TheProfessionnal/InfoClock/InfoClock-master/src/DisplayTask.cpp

/*
 * DisplayTask.cpp
 *
 *  Created on: 15.02.2017
 *      Author: Bartosz Bielawski
 */


#include "DisplayTask.hpp"

#include "pyfont.h"
#include "myTestFont8.h"

#include "utils.h"
#include "tasks_utils.h"
#include "DataStore.h"

#include "config.h"


DisplayTask::DisplayTask():
		TaskCRTP(&DisplayTask::nextMessage),
		ledMatrixDriver(
				readConfigWithDefault(F("segments"), "8").toInt(), LED_CS,
				readConfigWithDefault(F("rotation"), "0").toInt()),
				scroll(ledMatrixDriver),
		regularMessages({
			{this, getDate, 2_s,	1,	false},
			})
{
	init();
	ledMatrixDriver.setIntensity(readConfig(F("brightness")).toInt());
}


void DisplayTask::addClock()
{
	DisplayState ds = {this, getTime, 1_s, 5,	false};
	regularMessages.push_back(ds);
}


void DisplayTask::addRegularMessage(const DisplayState& ds)
{
	regularMessages.push_back(ds);
	addClock();
}

void DisplayTask::removeRegularMessages(void* owner)
{
	regularMessages.erase(
			std::remove_if(
					regularMessages.begin(),
					regularMessages.end(),
					[owner] (const DisplayState& ds) {return ds.owner == owner;}));
}

void DisplayTask::init()
{
	index = regularMessages.size()-1;
}

void DisplayTask::reset()
{
	init();
}


void DisplayTask::pushMessage(const String& m, uint16_t sleep, bool scrolling)
{
	priorityMessages.push_back(DisplayState{this, [m](){return m;}, sleep, 1, scrolling});

	//wake up thread and interrupt the other display
	//only if it's not a priority message
	if (!priorityMessagePlayed)
	{
		nextState = &DisplayTask::nextMessage;
		resume();
	}
}

void DisplayTask::scrollMessage()
{
	bool done = scroll.tick();
	sleep(ds.period);

	if (done)
	{
		logPrintfX(F("DT"), F("Scrolling done..."));
		nextState = &DisplayTask::nextMessage;
	}
}

void DisplayTask::nextMessage()
{
	//load the next display
	nextDisplay();

	if (ds.scrolling)
	{		
		scroll.renderString(currentMessage, myTestFont::font);
		nextState = &DisplayTask::scrollMessage;
		return;
	}

	nextState = &DisplayTask::refreshMessage;
}


void DisplayTask::refreshMessage()
{
	//this code here calls the function again and again because the message may be different every time
	//for example the time or date

	scroll.renderString(ds.fun(), myTestFont::font);

	if (--ds.cycles == 0)
		nextState = &DisplayTask::nextMessage;

	sleep(ds.period);
	//this flag will allow slow tasks to execute only if there is a two second sleep ahead
	slowTaskCanExecute = ds.period >= 1_s;
}


void DisplayTask::nextDisplay()
{
	//special case for priority messages
	if (priorityMessages.size())
	{
		ds = priorityMessages.front();
		priorityMessages.erase(priorityMessages.begin());
		currentMessage = ds.fun();
		
		logPrintfX(F("DT"), F("New message from PQ = %s"), currentMessage.c_str());
		priorityMessagePlayed = true;
		return;
	}

	priorityMessagePlayed = false;
	//otherwise get back to the regular display
		
	if (regularMessages.size() == 0)		
		return;
		
	do
	{
		index++;
		index %= regularMessages.size();
		ds = regularMessages[index];

		// save the current message for future use
		currentMessage = ds.fun();
	}
	while (currentMessage.length() == 0);	

	logPrintfX(F("DT"), F("New message from RQ = %s"), currentMessage.c_str());
	ledMatrixDriver.setIntensity(readConfig(F("brightness")).toInt());
}

DisplayTask& DisplayTask::getInstance()
{
	static DisplayTask displayTask;
	return displayTask;
}
