TheProfessionnal/InfoClock/InfoClock-master/src/WebServerTask.cpp

/*
 * WebServerTask.cpp
 *
 *  Created on: 10.01.2017
 *      Author: Bartosz Bielawski
 */

#include "Arduino.h"
#include "time.h"
#include "LittleFS.h"


#include "WebServerTask.h"
#include "ESP8266WebServer.h"
#include "ESP8266HTTPUpdateServer.h"
#include "ArduinoOTA.h"

#include "MacroStringReplace.h"
#include "config.h"
#include "DataStore.h"

#include "html/webpage.h"

#include "utils.h"
#include "tasks_utils.h"
#include "web_utils.h"
#include "LambdaTask.hpp"



WebServerTask::WebServerTask():
		webServer(80)
{
	reset();
	DisplayState ds{this, [this]() {return webmessage;}, 0.05_s, 1, true};
	addRegularMessage(ds);
}

void WebServerTask::registerPage(const String& url, const String& label,
		std::function<void(ESP8266WebServer& ws)> ph)
{
	registeredPages.emplace_back(url, label);
	String newUrl("/");
	newUrl += url;
	std::function<void(void)> f = [this, ph] () {ph(webServer);};
	webServer.on(newUrl.c_str(), f);
}

void WebServerTask::reset()
{
	webServer.stop();
	sleep(5_s);
	started = false;

	webmessage = "";
	webmessageIP = "";
}


void WebServerTask::run()
{
	if (!started)
	{
		started = true;
		logPrintfX(F("WST"), F("Configuring server"));

		webServer.onNotFound([this](){
			webServer.send(404, "text/plain", "Not found... :/");
		});

		webServer.on("/", [this](){
			handleMainPage();
		});

		webServer.on("/webmessage", [this](){handleWebMessage();});
		webServer.on("/status", 	[this](){handleStatus();});
		webServer.on("/reset", [this]{handleReset();});
		webServer.on("/config", [this]{handleConfig();});
		webServer.on("/log", [this](){handleLogs();});

		webServer.begin();

		logPrintfX(F("WST"), F("Ready!"));
		return;
	}

	webServer.handleClient();
	delay(0);
}

String WebServerTask::generateLinks()
{
	String results;

	for (auto& p: registeredPages)
	{
		results += "<a href=\"";
		results += p.first;
		results += "\">";
		results += p.second;
		results += "</a>\n";
	}

	return results;
}

FlashStream mainPageFS(mainPage);

void WebServerTask::handleMainPage()
{
	StringStream ss(2048);
	macroStringReplace(mainPageFS, [this] (const char*) {return generateLinks();}, ss);
	webServer.send(200, textHtml, ss.buffer);
}

FlashStream statusFS(statusPage);

void WebServerTask::handleStatus()
{
	StringStream ss(2048);
	macroStringReplace(pageHeaderFS, constString("Status"), ss);
	macroStringReplace(statusFS, dataSource, ss);
	webServer.send(200, textHtml, ss.buffer);
}


void WebServerTask::handleReset()
{
	if (!handleAuth(webServer)) return;

	rebootClock();

	webServer.sendHeader("Location", String("/"), true);
	webServer.send(302, textPlain, "");
}

void WebServerTask::handleLogs()
{
	if (!handleAuth(webServer)) return;

	StringStream ss(2048);
	webServer.chunkedResponseModeStart(200, "text/html");
	macroStringReplace(pageHeaderFS, constString("Logs"), ss);
	webServer.sendContent(ss.buffer);
	
	webServer.sendContent(F("<table>"));
	for (const auto& s: getLogHistory())
	{
		webServer.sendContent(F("<tr><td>"));
		webServer.sendContent(s);
		webServer.sendContent(F("</td></tr>\n\r"));
		
	}
	webServer.sendContent(F("</table><script>setTimeout(function(){window.location.reload(1);}, 5000);</script></body></html>"));
	webServer.chunkedResponseFinalize();
}

FlashStream webmessageFS(webmessagePage);

void WebServerTask::handleWebMessage()
{
	if (!handleAuth(webServer))
		return;

	if (webServer.method() == HTTP_POST)
	{
		auto wm = webServer.arg(F("webmessage"));
		
		webmessage = wm;
		webmessageIP = webServer.client().remoteIP().toString();
		logPrintfX(F("WST"),
				   F("New webmessage %s from %s"),
				   wm.c_str(),
				   webmessageIP.c_str());
	}

	StringStream ss(2048);

	macroStringReplace(pageHeaderFS, constString(F("Webmessage")), ss);
	macroStringReplace(webmessageFS, constString(webmessage), ss);

	webServer.send(200, textHtml, ss.buffer);
}

FlashStream configPageFS(configPage);

void WebServerTask::handleConfig()
{
	if (!handleAuth(webServer))
		return;

	String content;

	if (webServer.method() == HTTP_GET)
	{
		//read config from the file
		LittleFS.begin();
		auto file = LittleFS.open("/config.txt", "r");
		if (!file)
			content = F("# The file is empty, please create a new one!");
		else
		{
			content = file.readString();
			file.close();
		}
	
		LittleFS.end();
	}
	else
	{
		//POST
		//load content from variable
		content = webServer.arg(F("content"));
		LittleFS.begin();
		auto file = LittleFS.open("/config.txt", "w+");
		file.print(content);
		file.close();
		LittleFS.end();
		readConfigFromFS();
	}
	
	StringStream ss(2048);
	macroStringReplace(pageHeaderFS, constString(F("Config")), ss);
	macroStringReplace(configPageFS, constString(content), ss);
	webServer.send(200, textHtml, ss.buffer);
}

WebServerTask& WebServerTask::getInstance()
{
	static WebServerTask webServer;
	return webServer;
}
