TheProfessionnal/InfoClock/InfoClock-master/src/OTA.cpp

/*
 * OTA.cpp

 *
 *  Created on: 17.04.2017
 *      Author: caladan
 */

#include "Arduino.h"
#include "ArduinoOTA.h"
#include "pgmspace.h"
#include "OTA.hpp"
#include "utils.h"
#include "ESP8266mDNS.h"

void configureOTA()
{
	ArduinoOTA.onStart([]() {
		logPrintfX(F("OTA"), F("Starting..."));
	});

	ArduinoOTA.onEnd([]() {
		logPrintfX(F("OTA"), F("Done..."));
	});

	ArduinoOTA.onProgress([](unsigned int progress, unsigned int total) {
		logPrintfX(F("OTA"), F("Progress: %u%%"), (progress / (total / 100)));
	});
	ArduinoOTA.onError([](ota_error_t error) {
		logPrintfX(F("OTA"), F("Error[%u]"), error);
	});

	ArduinoOTA.setPassword(readConfig(F("configPassword")).c_str());

	ArduinoOTA.begin();
}
