TheProfessionnal/InfoClock/InfoClock-master/src/WeatherGetter.h

/*
 * WeatherGetter.h
 *
 *  Created on: 04.01.2017
 *      Author: Bartosz Bielawski
 */

#ifndef WEATHERGETTER_H_
#define WEATHERGETTER_H_

#include <tasks.hpp>
#include "ESP8266HTTPClient.h"
#include <vector>

#include <ESP8266WebServer.h>
class WeatherGetter: public Tasks::Task
{
	public:
		WeatherGetter();
		virtual ~WeatherGetter() {}
		virtual void reset();
		virtual void run();
	private:
		struct Weather
		{
			Weather(uint32_t locationId):
				locationId(locationId),
				temperature(0),
				temperatureForecast(0) {}

			uint32_t locationId;
			float  temperature;
			float  temperatureForecast;
			String description;
			String location;

		};

		std::vector<Weather> weathers;

		uint32_t currentWeatherIndex;

		String apiKey;

		//page handling
		void handleConfig(ESP8266WebServer& ws);
		void handleStatus(ESP8266WebServer& ws);

		//display function
		String getWeatherDescription();
};

#endif /* WEATHERGETTER_H_ */
