TheProfessionnal/InfoClock/InfoClock-master/src/myTestFont8.h

#ifndef myTestFont8_H
#define myTestFont8_H

#include "pyfont.h"

namespace myTestFont
{
    const uint8_t data[] =
    {
			0x00, 0x00, 0xBF, 0x03, 0x01, 0x03, 0x14, 0x3E, 0x14, 0x3E, 0x14, 0x2C, 0x7E, 0x34, 0x24, 0x10,
			0x08, 0x24, 0x60, 0x90, 0x90, 0x60, 0xF0, 0x10, 0x10, 0xE0, 0x90, 0x90, 0xFC, 0x03, 0x7E, 0x81,
			0x81, 0x7E, 0x14, 0x08, 0x14, 0x08, 0x08, 0x3E, 0x08, 0x08, 0xC0, 0x08, 0x08, 0x08, 0x80, 0x60,
			0x18, 0x06, 0x7E, 0x99, 0x8D, 0x7E, 0x04, 0x82, 0xFF, 0x80, 0xE2, 0x91, 0x89, 0x86, 0x42, 0x89,
			0x89, 0x76, 0x0F, 0x08, 0x08, 0xFF, 0x8F, 0x89, 0x89, 0x71, 0x7E, 0x89, 0x89, 0x72, 0x01, 0xF1,
			0x09, 0x07, 0x76, 0x89, 0x89, 0x76, 0x46, 0x89, 0x89, 0x7E, 0x24, 0xC4, 0x08, 0x14, 0x22, 0x14,
			0x14, 0x14, 0x14, 0x22, 0x14, 0x08, 0x02, 0x01, 0xB1, 0x0E, 0x38, 0x44, 0x92, 0xAA, 0xF2, 0x84,
			0x78, 0xFE, 0x09, 0x09, 0xFE, 0xFF, 0x89, 0x89, 0x76, 0x7E, 0x81, 0x81, 0x46, 0xFF, 0x81, 0x81,
			0x7E, 0xFF, 0x89, 0x89, 0x81, 0xFF, 0x09, 0x09, 0x01, 0x7E, 0x81, 0x89, 0x7A, 0xFF, 0x08, 0x08,
			0xFF, 0xFF, 0x41, 0x81, 0x81, 0x7F, 0xFF, 0x08, 0x14, 0xE3, 0xFF, 0x80, 0x80, 0x80, 0xFF, 0x02,
			0x04, 0x02, 0xFF, 0xFF, 0x02, 0x04, 0x08, 0xFF, 0x7E, 0x81, 0x81, 0x7E, 0xFF, 0x09, 0x09, 0x06,
			0x7E, 0x81, 0xC1, 0xFE, 0xFF, 0x09, 0x09, 0xF6, 0x46, 0x89, 0x89, 0x72, 0x01, 0x01, 0xFF, 0x01,
			0x01, 0x7F, 0x80, 0x80, 0x7F, 0x3F, 0x40, 0x80, 0x40, 0x3F, 0xFF, 0x40, 0x20, 0x40, 0xFF, 0xE3,
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
			0x04, 0x04, 0x04, 0x04, 0x04, 0x04, 0x07, 0x04, 0x04, 0x04, 0x04, 0x04, 0x02, 0x02, 0x03, 0x03,
			0x04, 0x04, 0x04, 0x04, 0x04, 0x04, 0x04, 0x05, 0x04, 0x04, 0x04, 0x04, 0x04, 0x04, 0x05, 0x04
    };

    const PyFont font(224, 32, data, offsets, sizes);
}

#endif //myTestFont_H
