TheProfessionnal/InfoClock/InfoClock-master/src/web_utils.h

/*
 * web_utils.h
 *
 *  Created on: 04.05.2017
 *      Author: caladan
 */

#ifndef WEB_UTILS_H_
#define WEB_UTILS_H_

#include "MacroStringReplace.h"
#include <ESP8266WebServer.h>
#include <functional>

void registerPage(const String& url, const String& label, std::function<void(ESP8266WebServer&)> ph);
bool handleAuth(ESP8266WebServer& webServer);
extern FlashStream pageHeaderFS;

extern const char textPlain[];
extern const char textHtml[];


#endif /* WEB_UTILS_H_ */
